SimonRafferty/Td5-Diagnostic-App/Firmware/Td5_Diagnostic/td5comm.h

/*
Td5Comm.h -
 
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
 */

#ifndef Td5Comm_h
#define Td5Comm_h

#include <Arduino.h>

#define _FAULT_CODES_STRINGS_

#define Td5RequestByteDelay       1
#define Td5RequestDelay           55
#define Td5KeepAliveDelay         4000L

#define READ_ATTEMPTS             7
#define FRAME_READ_ATTEMPT_TIME   300
#define INIT_FIRST_DELAY_TIME     300
#define MAX_FAULT_CODE            280
#define MAX_FUELLING_PARAMS       22
#define KEEP_ALIVE_TIME           4500

#define INIT_FRAME      0x00
#define START_DIAG      0x01
#define REQ_SEED        0x02
#define SEND_KEY        0x03
#define START_FUELLING  0x04
#define ENGINE_RPM      0x05
#define TEMPERATURES    0x06
#define INLET_PRES_MAF  0x07
#define BATTERY_VOLT    0x08
#define AMBIENT_PRES    0x09
#define VEHICLE_SPEED   0x0A
#define THROTTLE_POS    0x0B
#define IO_CONTROL      0x0C
#define INJ_BALANCE     0x0D
#define RPM_ERROR       0x0E
#define EGR_MOD         0x0F
#define ILT_MOD         0x10
#define TWG_MOD         0x11
#define KEEP_ALIVE      0x12
#define FAULT_CODES     0x13
#define CLEAR_FAULTS    0x14
#define FUELLING        0x15
#define CRUISE_SWITCHES 0x16   // PID 0x1E - Cruise/Brake switches (Nanocom-validated)
#define DIGITAL_INPUTS  0x0E   // Alias: RPM_ERROR is actually Idle Speed Error (0x21)
#define IDLE_ERROR      0x0E   // Alias: PID 0x21 = Idle Speed Error (signed RPM)
#define RELAY_OUTPUTS   0x17   // PID 0x36 - relay/output status bitfield
#define EGR_INLET       0x18   // PID 0x45 - EGR inlet throttle (%)
#define VIN_READ        0x19   // Service 0x1A id 0x87 - VIN (flash ECUs only)
#define MAP_NAME        0x1A   // PID 0x32 - map/fuel/homologation strings

class Td5Pid;

// Class Td5Comm
class Td5Comm
{
public:
  Td5Comm();
  void init();
  void initComm();
  // respTimeoutMs: how long (from the start of the request) to wait for the reply.
  // 300 ms suits every live-data PID; the clear-faults routine needs longer.
  int8_t getPid(Td5Pid* pid, uint16_t respTimeoutMs = 300);
  bool ecuIsConnected();
  bool newDataIsAvailable();
  unsigned long getLastReceivedPidTime();
  unsigned long getLastReceivedPidElapsedTime();
  void setInitStep(byte init_step);
  byte getInitStep();
  int getLostFrames();
  int getConsecutiveLostFrames();

  bool connectToEcu(bool showBar = true);
  void disconnectFromEcu();
  int getFaultCodes();
  int getFaultCode(int index);
  int getFaultCodesCount(){return faultCodesCount;};
  int8_t resetFaults();
  
private:  
  byte checksum(byte *data, byte len);
  bool read_byte(byte * b);
  void write_byte(byte b);

protected:
  unsigned long lastReceivedPidTime;
  unsigned long initTime;
  byte initStep;  // Init is multistage, this is the counter
  bool ecuConnection;  // Have we connected to the ECU or not
  bool newDataAvailable;
  int lostFrames;
  int8_t consLostFrames;
  int faultCodesCount;
};

// Class Td5Pid
class Td5Pid
{
public:
  Td5Pid(byte ID, byte reqlen, byte resplen, long cycletime = 0);
  void setCycleTime(long time){ cycleTime = time; };
  bool getValue(float *fvalue, byte index = 0);
  bool getValue(uint16_t *value, byte index = 0);
  bool getValue(int *value, byte index = 0);
  float getfValue(byte index = 0);
  uint16_t getulValue(byte index = 0);
  int16_t getlValue(byte index = 0);
  byte getbValue(byte index = 0);
  
  void setRequestByte(byte value, byte pos);
  byte getResponseByte(byte pos);

  byte *requestFrame;
  byte *responseFrame;
  
  byte id;
  long cycleTime;
  long lastSeenTime;
  byte responseLength;  
};

// Generic functions
void remote_log_byte(byte b);
void remote_log_frame(byte *datasent, byte sentlen, byte *datarecv, byte recvlen);
void retrieve_keys_from_eeprom(uint8_t *seed, uint8_t *key);

uint8_t td5_get_next_fault_code();
uint8_t td5_get_previous_fault_code();
   

// Declare pids
extern Td5Pid pidInitFrame;
extern Td5Pid pidStartDiag;
extern Td5Pid pidRequestSeed;
extern Td5Pid pidSendKey;
extern Td5Pid pidRPM;
extern Td5Pid pidTurboPressureMaf;
extern Td5Pid pidTemperatures;
extern Td5Pid pidBatteryVoltage;
extern Td5Pid pidAmbientPressure;
extern Td5Pid pidStartFuelling;
extern Td5Pid pidKeepAlive;
extern Td5Pid pidFaultCodes;
extern Td5Pid pidResetFaults;
extern Td5Pid pidInjectorsBalance;
extern Td5Pid pidVehicleSpeed;
extern Td5Pid pidThrottlePosition;
extern Td5Pid pidDigitalInputs;      // 0x21 - brake/clutch/handbrake/etc
extern Td5Pid pidCruiseBrakeSwitches; // 0x1E - cruise control switches
extern Td5Pid pidEGR;
extern Td5Pid pidILT;
extern Td5Pid pidTWG;
extern Td5Pid pidFuelling;
extern Td5Pid pidRelayOutputs;   // 0x36 - relay/output status bitfield
extern Td5Pid pidEgrInlet;       // 0x45 - EGR inlet throttle
extern Td5Pid pidVin;            // 1A 87 - VIN
extern Td5Pid pidMapName;        // 21 32 - map/fuel/homologation

#define PID_NOT_READY        0
#define PID_LOST_FRAME      -1
#define PID_NEGATIVE_ANSWER -2

#endif
